danbaker-projects/vistaECP/kicad/vistaECP/3dModels/kicad-SMD-Diode-b340.fcstd

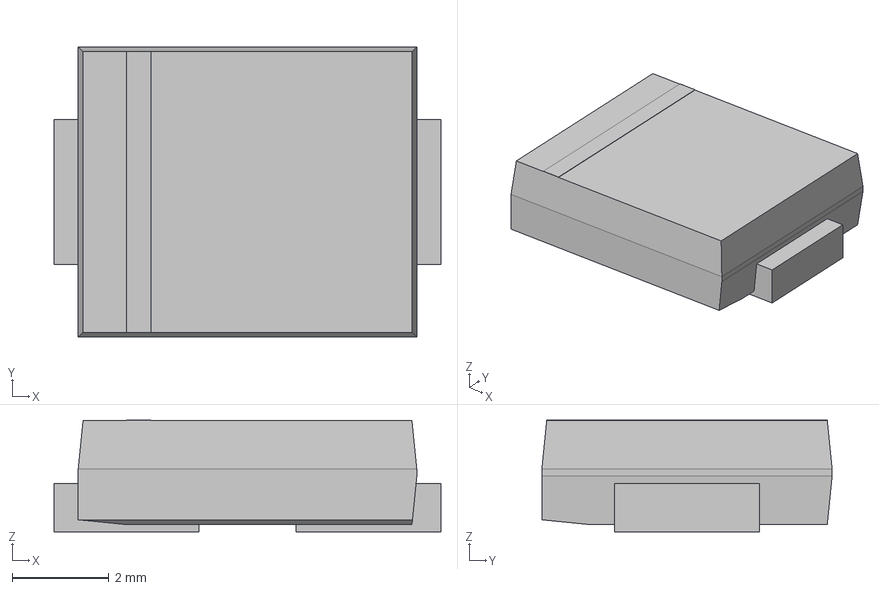
[picture p20: CAD file, 2026-10-01]
kicad/vistaECP/3dModels/kicad-SMD-Diode-b340.fcstd
8.00 x 6.00 x 2.31 mm
